djvs/m0116/m0116.kicad_sch

## KiCad design m0116.kicad_sch (2023-02-25)

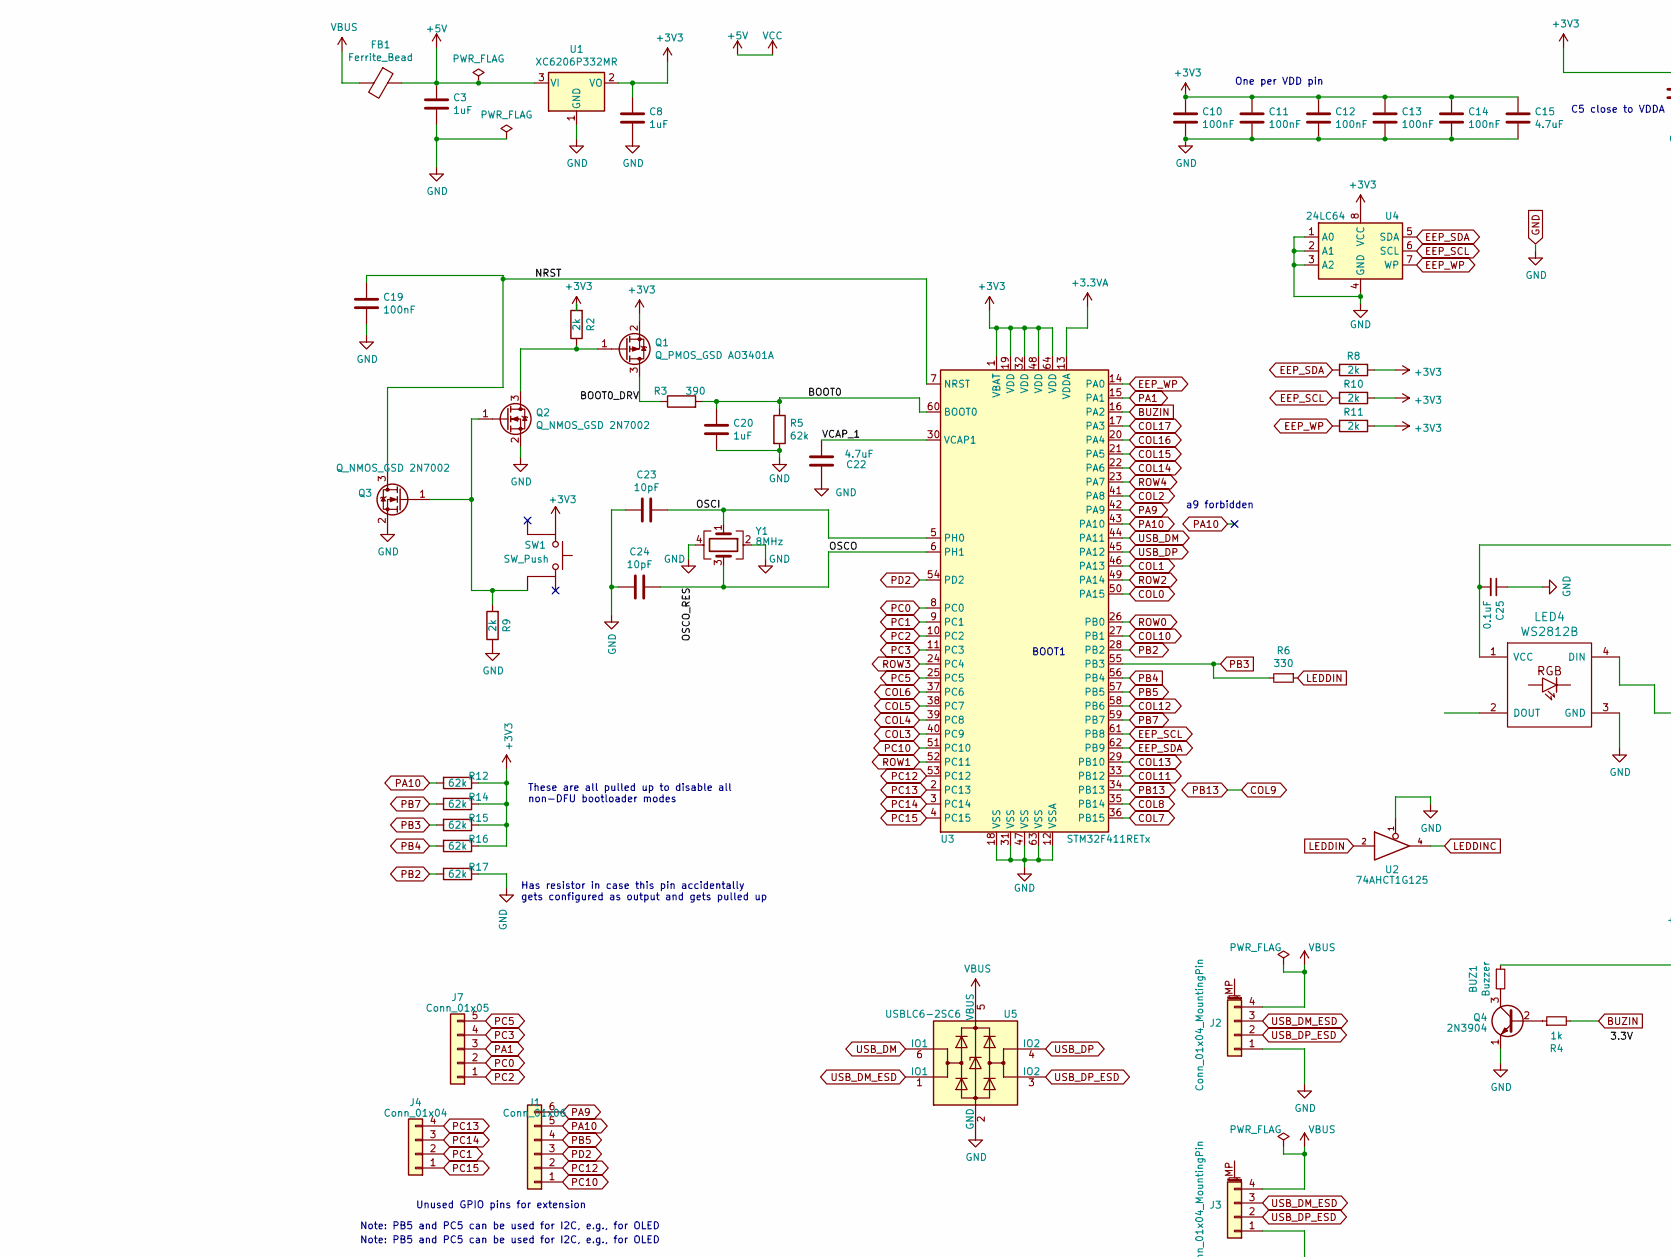
[picture p10: schematic m0116.kicad_sch, part in row 1, column 1]

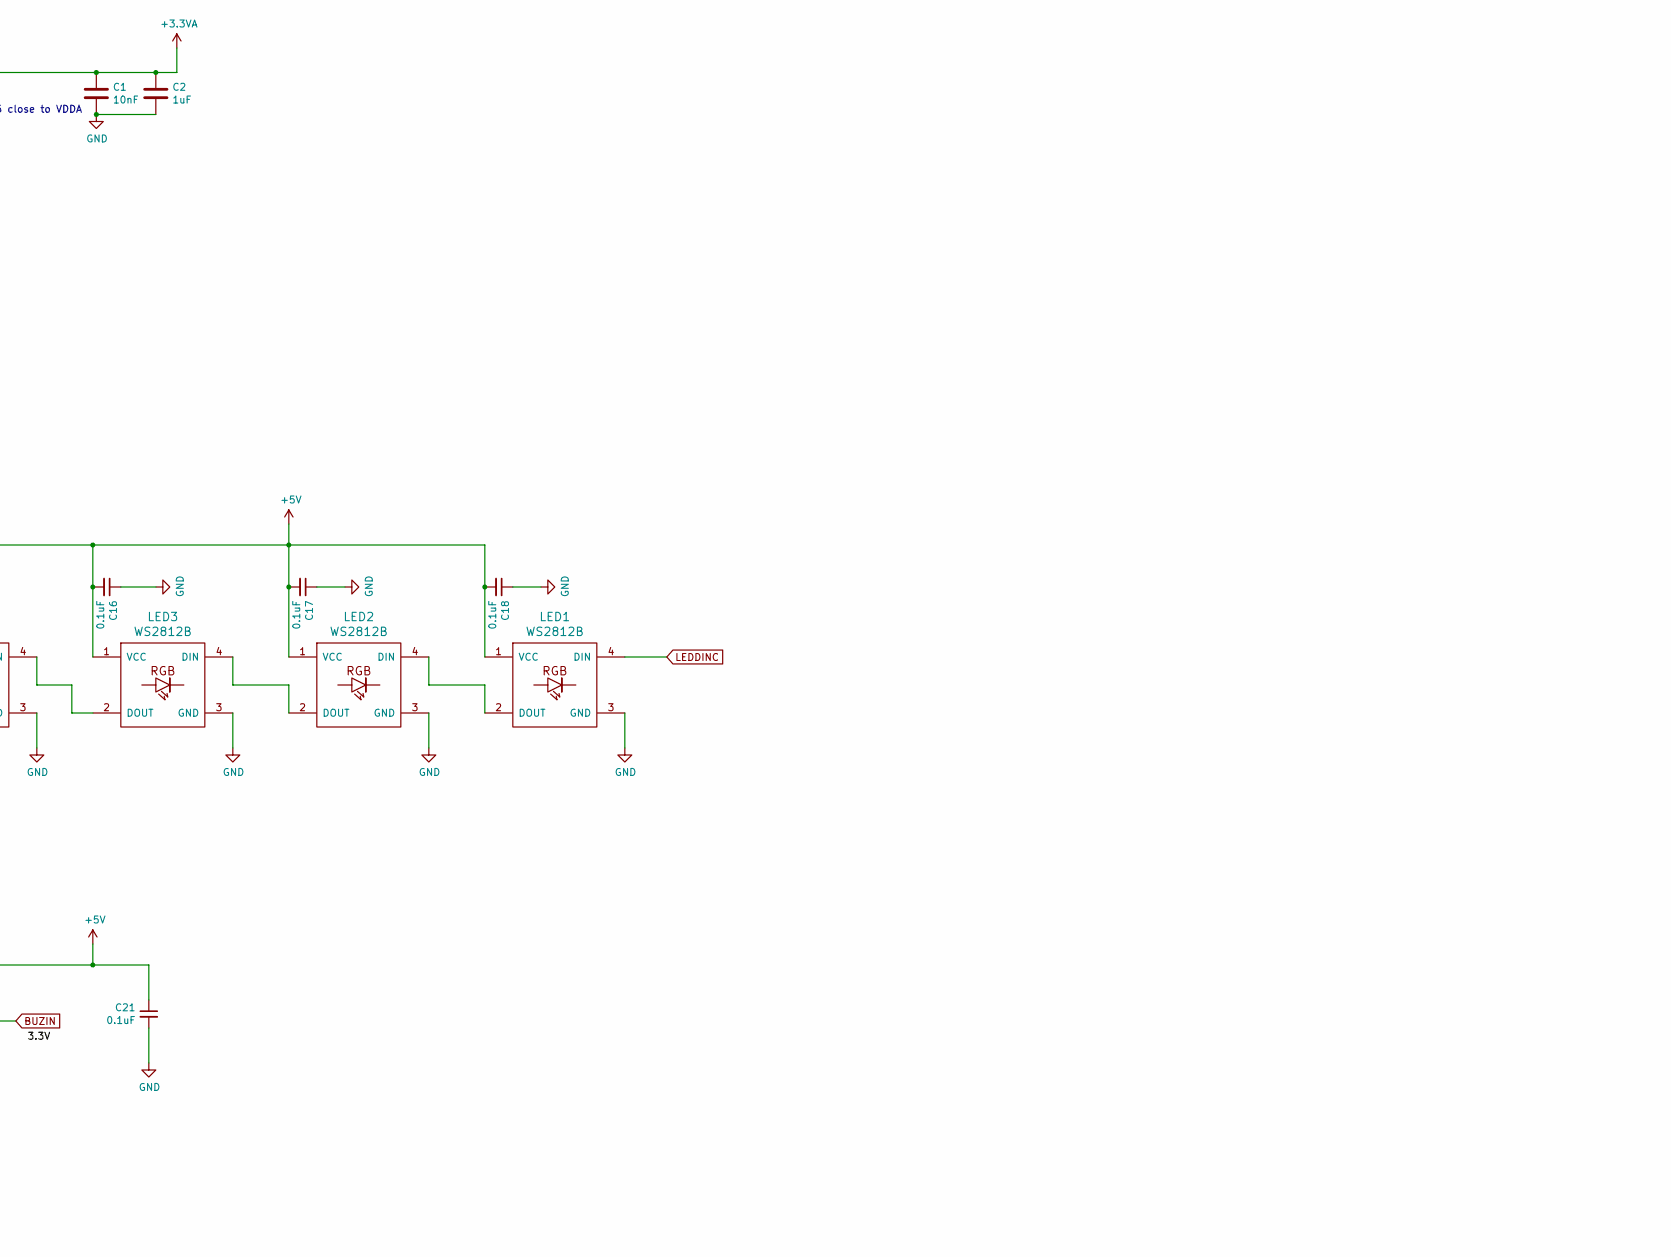
[picture p11: schematic m0116.kicad_sch, part in row 1, column 2]

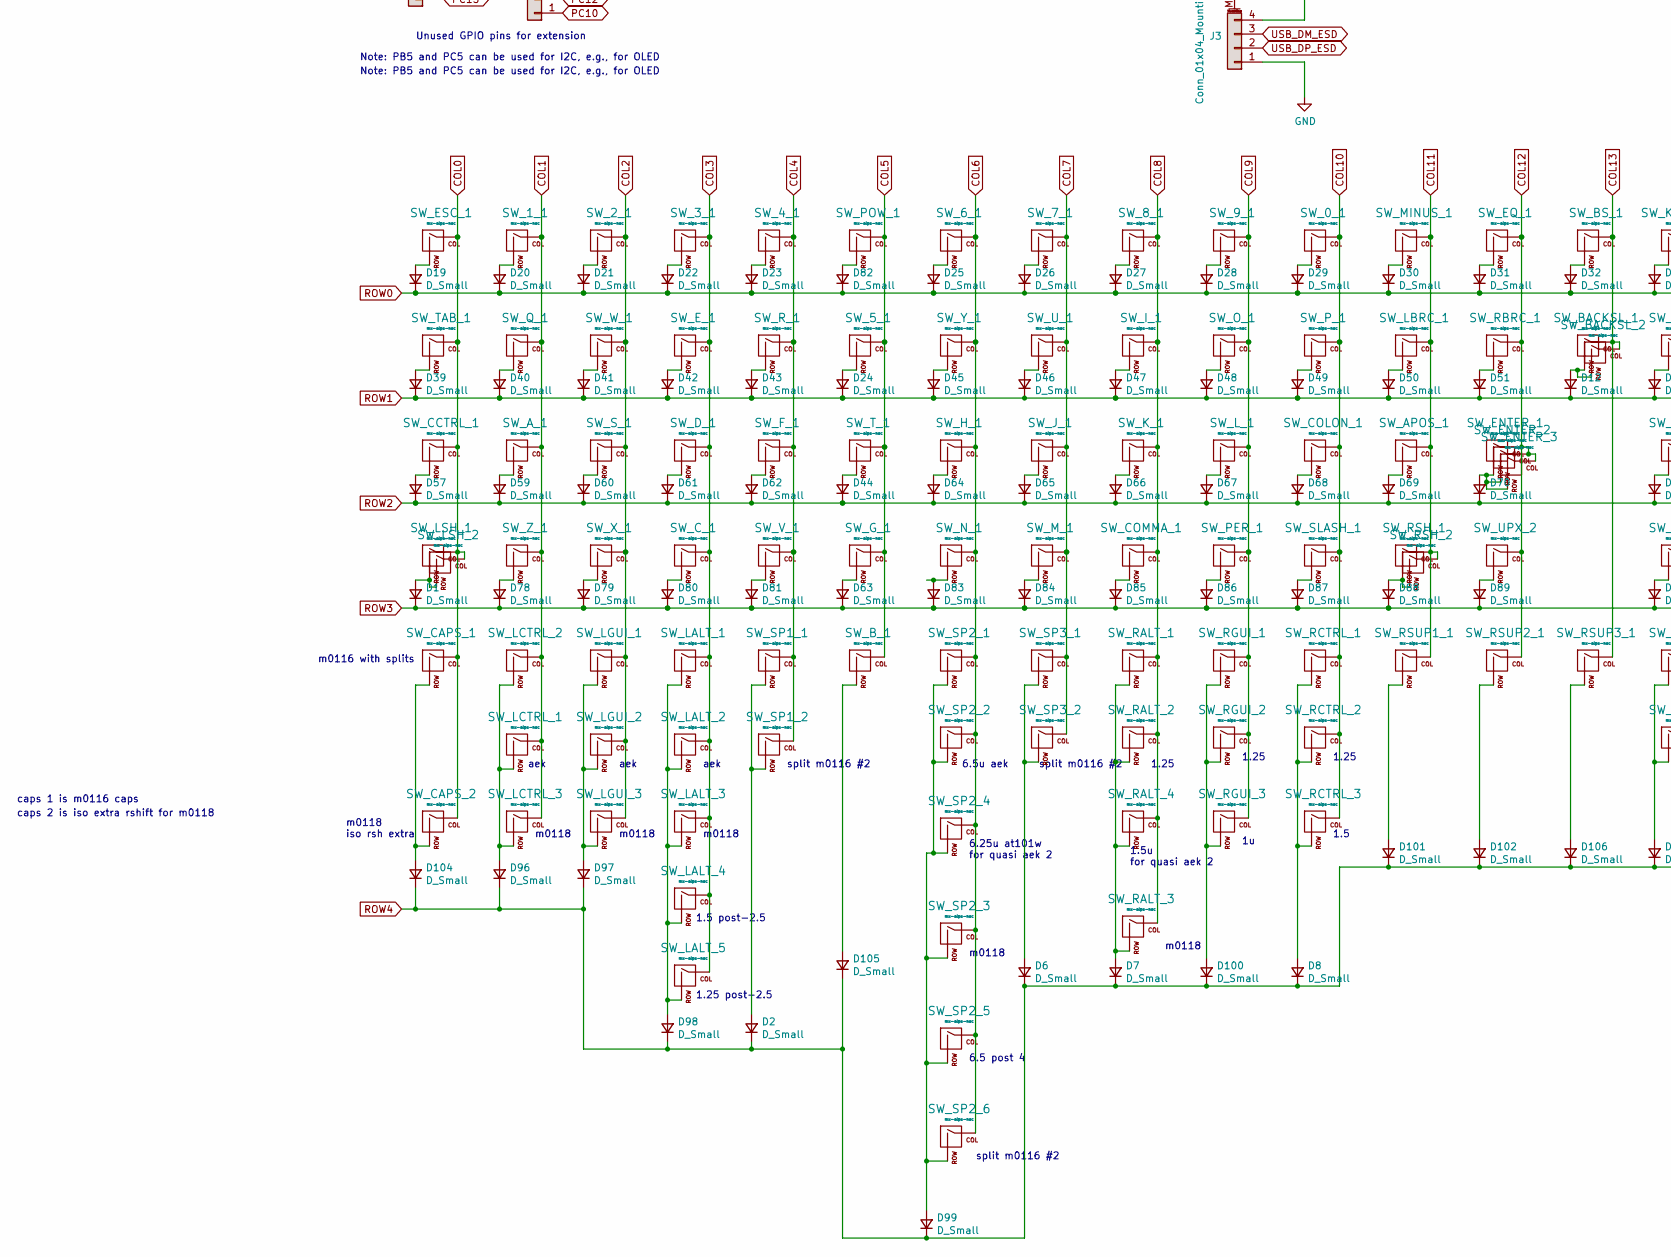
[picture p12: schematic m0116.kicad_sch, part in row 2, column 1]

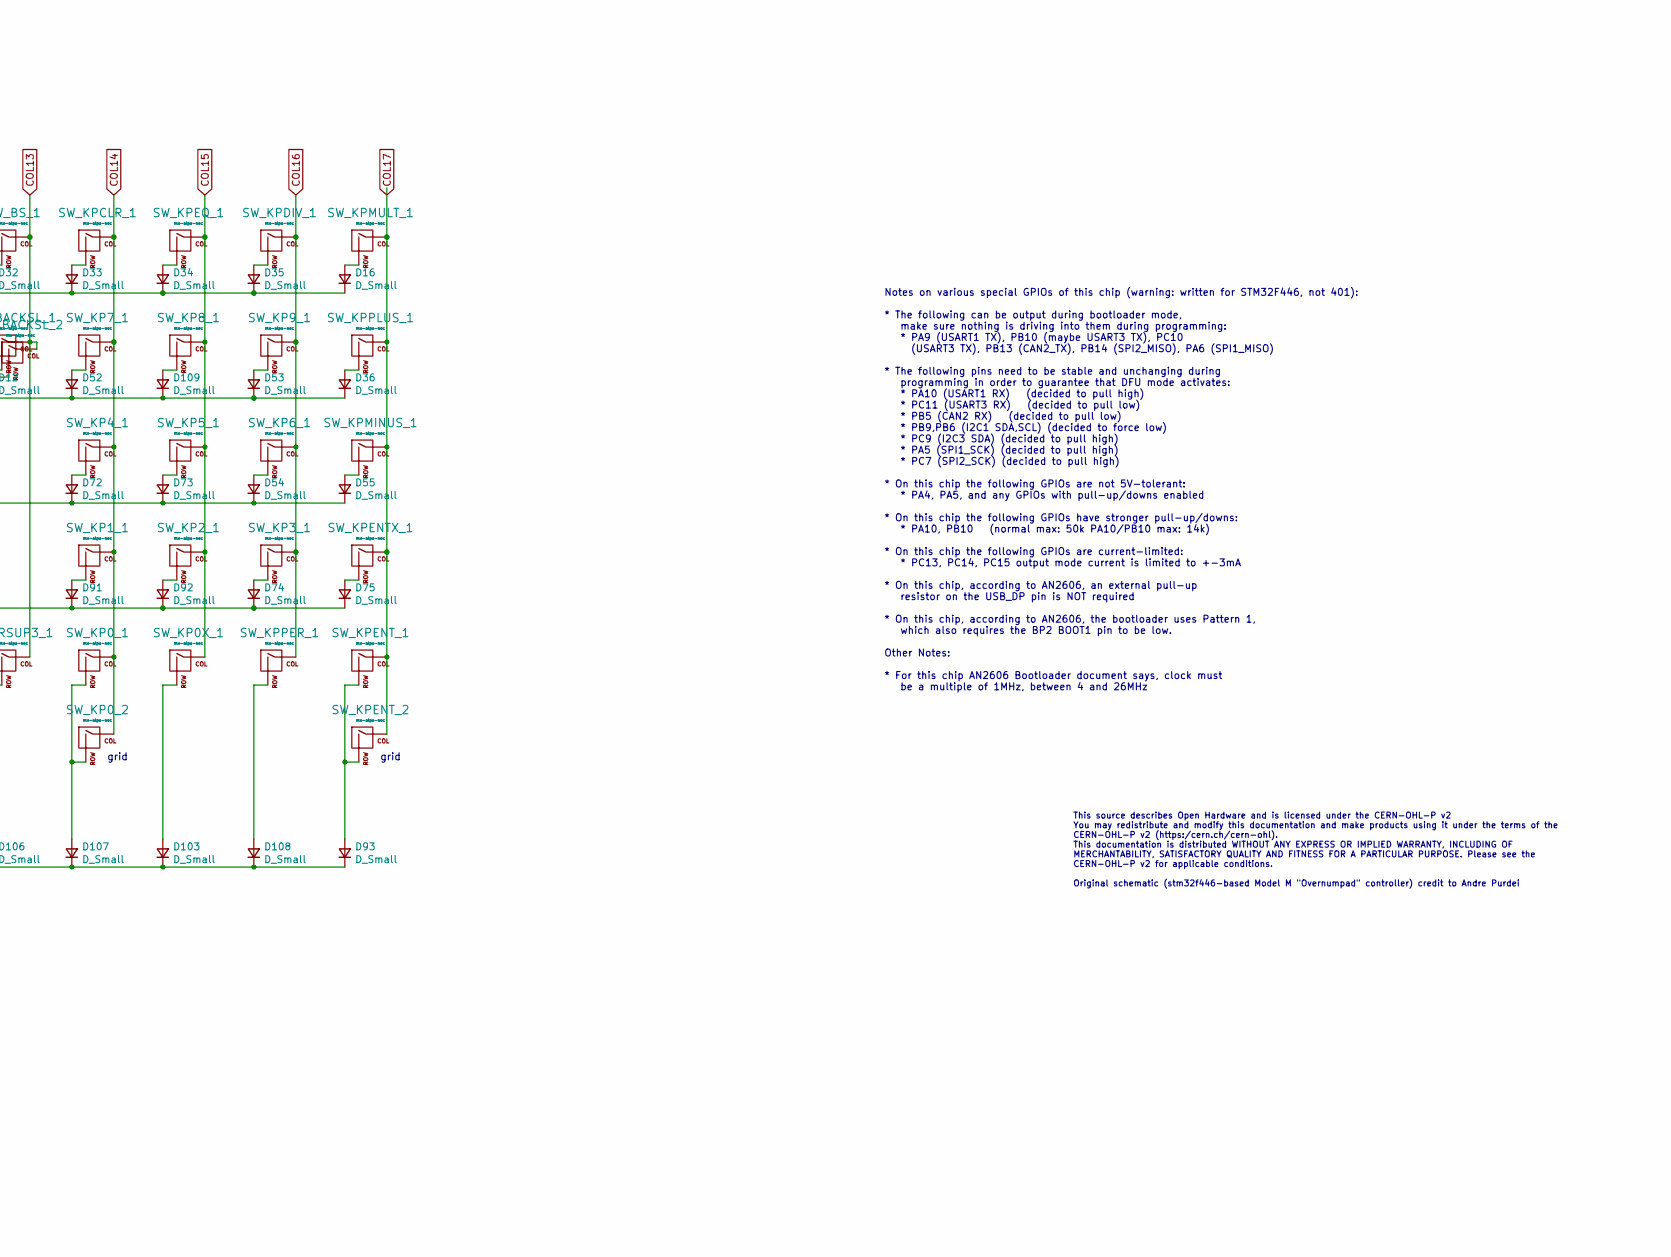
[picture p13: schematic m0116.kicad_sch, part in row 2, column 2]

Parts:
BUZ1: Buzzer; Buzzer_Mallory_AST1109MLTRQ
C1: 10nF; C_0805_2012Metric_Pad1.18x1.45mm_HandSolder; LCSC C1710
C2, C3, C20: 1uF; C_0805_2012Metric_Pad1.18x1.45mm_HandSolder; LCSC C28323
C8: 1uF; C_0805_2012Metric_Pad1.18x1.45mm_HandSolder; LCSC C49678
C10, C11, C12, C13, C14, C19: 100nF; C_0805_2012Metric_Pad1.18x1.45mm_HandSolder; LCSC C49678
C15, C22: 4.7uF; C_0805_2012Metric_Pad1.18x1.45mm_HandSolder; LCSC C1779
C16, C17, C18, C21, C25: 0.1uF; C_0805_2012Metric
C23, C24: 10pF; C_0805_2012Metric_Pad1.18x1.45mm_HandSolder; LCSC C1785
D1, D2, D6, D7, D8, D12, D16, D19, D20, D21, D22, D23, D24, D25, D26, D27, D28, D29, D30, D31, D32, D33, D34, D35, D36, D39, D40, D41, D42, D43, D44, D45, D46, D47, D48, D49, D50, D51, D52, D53, D54, D55, D57, D59, D60, D61, D62, D63, D64, D65, D66, D67, D68, D69, D70, D72, D73, D74, D75, D78, D79, D80, D81, D82, D83, D84, D85, D86, D87, D88, D89, D91, D92, D93, D96, D97, D98, D99, D100, D101, D102, D103, D104, D105, D106, D107, D108, D109: D_Small; D_SOD-123
FB1: Ferrite_Bead; L_0805_2012Metric_Pad1.15x1.40mm_HandSolder; LCSC C1015
J1: Conn_01x06; PinHeader_1x06_P1.27mm_Vertical
J2, J3: Conn_01x04_MountingPin; JST_SH_SM04B-SRSS-TB_1x04-1MP_P1.00mm_Horizontal
J4: Conn_01x04; PinHeader_1x04_P1.27mm_Vertical
J7: Conn_01x05; PinHeader_1x05_P1.27mm_Vertical
LED1, LED2, LED3, LED4: WS2812B; WS2812BDual
Q1: Q_PMOS_GSD AO3401A; SOT-23; LCSC C700954
Q2, Q3: Q_NMOS_GSD 2N7002; SOT-23; LCSC C8545
Q4: 2N3904; SOT-23
R2, R8, R9, R10, R11: 2k; R_0805_2012Metric_Pad1.20x1.40mm_HandSolder; LCSC C17604
R3: 390; R_0805_2012Metric_Pad1.20x1.40mm_HandSolder; LCSC C17655
R4: 1k; R_0805_2012Metric
R5, R12, R14, R15, R16, R17: 62k; R_0805_2012Metric_Pad1.20x1.40mm_HandSolder; LCSC C17783
R6: 330; R_0805_2012Metric
SW1: SW_Push; switch_K2-1187SQ-A4SW-06; LCSC C92584
SW_0_1, SW_1_1, SW_2_1, SW_3_1, SW_4_1, SW_5_1, SW_6_1, SW_7_1, SW_8_1, SW_9_1: mx-alps-nec; ALPS-1U
SW_APOS_1: mx-alps-nec; ALPS-1U
SW_A_1: mx-alps-nec; ALPS-1U
SW_BACKSL_1, SW_BACKSL_2: mx-alps-nec; ALPS-1U
SW_BS_1: mx-alps-nec; ALPS-1U
SW_B_1: mx-alps-nec; ALPS-1U
SW_CAPS_1, SW_CAPS_2: mx-alps-nec; ALPS-1U
SW_CCTRL_1: mx-alps-nec; ALPS-1U
SW_COLON_1: mx-alps-nec; ALPS-1U
SW_COMMA_1: mx-alps-nec; ALPS-1U
SW_C_1: mx-alps-nec; ALPS-1U
SW_D_1: mx-alps-nec; ALPS-1U
SW_ENTER_1, SW_ENTER_2, SW_ENTER_3: mx-alps-nec; ALPS-1U
SW_EQ_1: mx-alps-nec; ALPS-1U
SW_ESC_1: mx-alps-nec; ALPS-1U
SW_E_1: mx-alps-nec; ALPS-1U
SW_F_1: mx-alps-nec; ALPS-1U
SW_G_1: mx-alps-nec; ALPS-1U
SW_H_1: mx-alps-nec; ALPS-1U
SW_I_1: mx-alps-nec; ALPS-1U
SW_J_1: mx-alps-nec; ALPS-1U
SW_KP0X_1, SW_KP0_1, SW_KP0_2, SW_KP1_1, SW_KP2_1, SW_KP3_1, SW_KP4_1, SW_KP5_1, SW_KP6_1, SW_KP7_1, SW_KP8_1, SW_KP9_1: mx-alps-nec; ALPS-1U
SW_KPCLR_1: mx-alps-nec; ALPS-1U
SW_KPDIV_1: mx-alps-nec; ALPS-1U
SW_KPENTX_1: mx-alps-nec; ALPS-1U
SW_KPENT_1, SW_KPENT_2: mx-alps-nec; ALPS-1U
SW_KPEQ_1: mx-alps-nec; ALPS-1U
SW_KPMINUS_1: mx-alps-nec; ALPS-1U
SW_KPMULT_1: mx-alps-nec; ALPS-1U
SW_KPPER_1: mx-alps-nec; ALPS-1U
SW_KPPLUS_1: mx-alps-nec; ALPS-1U
SW_K_1: mx-alps-nec; ALPS-1U
SW_LALT_1, SW_LALT_2, SW_LALT_3, SW_LALT_4, SW_LALT_5: mx-alps-nec; ALPS-1U
SW_LBRC_1: mx-alps-nec; ALPS-1U
SW_LCTRL_1, SW_LCTRL_2, SW_LCTRL_3: mx-alps-nec; ALPS-1U
SW_LGUI_1, SW_LGUI_2, SW_LGUI_3: mx-alps-nec; ALPS-1U
SW_LSH_1, SW_LSH_2: mx-alps-nec; ALPS-1U
SW_L_1: mx-alps-nec; ALPS-1U
SW_MINUS_1: mx-alps-nec; ALPS-1U
SW_M_1: mx-alps-nec; ALPS-1U
SW_N_1: mx-alps-nec; ALPS-1U
SW_O_1: mx-alps-nec; ALPS-1U
SW_PER_1: mx-alps-nec; ALPS-1U
SW_POW_1: mx-alps-nec; ALPS-1U
SW_P_1: mx-alps-nec; ALPS-1U
SW_Q_1: mx-alps-nec; ALPS-1U
SW_RALT_1, SW_RALT_2, SW_RALT_3, SW_RALT_4: mx-alps-nec; ALPS-1U
SW_RBRC_1: mx-alps-nec; ALPS-1U
SW_RCTRL_1, SW_RCTRL_2, SW_RCTRL_3: mx-alps-nec; ALPS-1U
SW_RGUI_1, SW_RGUI_2, SW_RGUI_3: mx-alps-nec; ALPS-1U
SW_RSH_1, SW_RSH_2: mx-alps-nec; ALPS-1U
SW_RSUP1_1, SW_RSUP2_1, SW_RSUP3_1: mx-alps-nec; ALPS-1U
SW_R_1: mx-alps-nec; ALPS-1U
SW_SLASH_1: mx-alps-nec; ALPS-1U
SW_SP1_1, SW_SP1_2, SW_SP2_1, SW_SP2_2, SW_SP2_3, SW_SP2_4, SW_SP2_5, SW_SP2_6, SW_SP3_1, SW_SP3_2: mx-alps-nec; ALPS-1U
SW_S_1: mx-alps-nec; ALPS-1U
SW_TAB_1: mx-alps-nec; ALPS-1U
SW_T_1: mx-alps-nec; ALPS-1U
SW_UPX_2: mx-alps-nec; ALPS-1U
SW_U_1: mx-alps-nec; ALPS-1U
SW_V_1: mx-alps-nec; ALPS-1U
SW_W_1: mx-alps-nec; ALPS-1U
SW_X_1: mx-alps-nec; ALPS-1U
SW_Y_1: mx-alps-nec; ALPS-1U
SW_Z_1: mx-alps-nec; ALPS-1U
U1: XC6206P332MR; SOT-23_Handsoldering; LCSC C6186
U2: 74AHCT1G125; SOT-23-5
U3: STM32F411RETx; LQFP-64_10x10mm_P0.5mm; LCSC C69336
U4: 24LC64; SOIC-8_3.9x4.9mm_P1.27mm; LCSC C79988
U5: USBLC6-2SC6; SOT-23-6; LCSC C7519
Y1: 8MHz; Crystal_SMD_3225-4Pin_3.2x2.5mm; LCSC C389817

Connections:
+3.3VA: C1.1, C2.1, C8.1, C10.1, C11.1, C12.1, C13.1, C14.1, C15.1, Q1.2 (S), R2.2, R8.1, R10.1, R11.1, R12.1, R14.1, R15.1, R16.1, SW1.1, U1.2 (VO), U3.1 (VBAT), U3.13 (VDDA), U3.19 (VDD), U3.32 (VDD), U3.48 (VDD), U3.64 (VDD), U4.8 (VCC)
+5V: BUZ1.1, C3.1, C16.2, C17.2, C18.2, C21.1, C25.2, FB1.1, LED1.1 (VCC), LED2.1 (VCC), LED3.1 (VCC), LED4.1 (VCC), U1.3 (VI)
BOOT0: C20.1, R3.2, R5.1, U3.60 (BOOT0)
BOOT0_DRV: Q1.3 (D), R3.1
BUZIN: R4.2, U3.16 (PA2)
COL0: SW_CAPS_1.1 (COL), SW_CAPS_2.1 (COL), SW_CCTRL_1.1 (COL), SW_ESC_1.1 (COL), SW_LSH_1.1 (COL), SW_LSH_2.1 (COL), SW_TAB_1.1 (COL), U3.50 (PA15)
COL1: SW_1_1.1 (COL), SW_A_1.1 (COL), SW_LCTRL_1.1 (COL), SW_LCTRL_2.1 (COL), SW_LCTRL_3.1 (COL), SW_Q_1.1 (COL), SW_Z_1.1 (COL), U3.46 (PA13)
COL2: SW_2_1.1 (COL), SW_LGUI_1.1 (COL), SW_LGUI_2.1 (COL), SW_LGUI_3.1 (COL), SW_S_1.1 (COL), SW_W_1.1 (COL), SW_X_1.1 (COL), U3.41 (PA8)
COL3: SW_3_1.1 (COL), SW_C_1.1 (COL), SW_D_1.1 (COL), SW_E_1.1 (COL), SW_LALT_1.1 (COL), SW_LALT_2.1 (COL), SW_LALT_3.1 (COL), SW_LALT_4.1 (COL), SW_LALT_5.1 (COL), U3.40 (PC9)
COL4: SW_4_1.1 (COL), SW_F_1.1 (COL), SW_R_1.1 (COL), SW_SP1_1.1 (COL), SW_SP1_2.1 (COL), SW_V_1.1 (COL), U3.39 (PC8)
COL5: SW_5_1.1 (COL), SW_B_1.1 (COL), SW_G_1.1 (COL), SW_POW_1.1 (COL), SW_T_1.1 (COL), U3.38 (PC7)
COL6: SW_6_1.1 (COL), SW_H_1.1 (COL), SW_N_1.1 (COL), SW_SP2_1.1 (COL), SW_SP2_2.1 (COL), SW_SP2_3.1 (COL), SW_SP2_4.1 (COL), SW_SP2_5.1 (COL), SW_SP2_6.1 (COL), SW_Y_1.1 (COL), U3.37 (PC6)
COL7: SW_7_1.1 (COL), SW_J_1.1 (COL), SW_M_1.1 (COL), SW_SP3_1.1 (COL), SW_SP3_2.1 (COL), SW_U_1.1 (COL), U3.36 (PB15)
COL8: SW_8_1.1 (COL), SW_COMMA_1.1 (COL), SW_I_1.1 (COL), SW_K_1.1 (COL), SW_RALT_1.1 (COL), SW_RALT_2.1 (COL), SW_RALT_3.1 (COL), SW_RALT_4.1 (COL), U3.35 (PB14)
COL9: SW_9_1.1 (COL), SW_L_1.1 (COL), SW_O_1.1 (COL), SW_PER_1.1 (COL), SW_RGUI_1.1 (COL), SW_RGUI_2.1 (COL), SW_RGUI_3.1 (COL), U3.34 (PB13)
COL10: SW_0_1.1 (COL), SW_COLON_1.1 (COL), SW_P_1.1 (COL), SW_RCTRL_1.1 (COL), SW_RCTRL_2.1 (COL), SW_RCTRL_3.1 (COL), SW_SLASH_1.1 (COL), U3.27 (PB1)
COL11: SW_APOS_1.1 (COL), SW_LBRC_1.1 (COL), SW_MINUS_1.1 (COL), SW_RSH_1.1 (COL), SW_RSH_2.1 (COL), SW_RSUP1_1.1 (COL), U3.33 (PB12)
COL12: SW_ENTER_1.1 (COL), SW_ENTER_2.1 (COL), SW_ENTER_3.1 (COL), SW_EQ_1.1 (COL), SW_RBRC_1.1 (COL), SW_RSUP2_1.1 (COL), SW_UPX_2.1 (COL), U3.58 (PB6)
COL13: SW_BACKSL_1.1 (COL), SW_BACKSL_2.1 (COL), SW_BS_1.1 (COL), SW_RSUP3_1.1 (COL), U3.29 (PB10)
COL14: SW_KP0_1.1 (COL), SW_KP0_2.1 (COL), SW_KP1_1.1 (COL), SW_KP4_1.1 (COL), SW_KP7_1.1 (COL), SW_KPCLR_1.1 (COL), U3.22 (PA6)
COL15: SW_KP0X_1.1 (COL), SW_KP2_1.1 (COL), SW_KP5_1.1 (COL), SW_KP8_1.1 (COL), SW_KPEQ_1.1 (COL), U3.21 (PA5)
COL16: SW_KP3_1.1 (COL), SW_KP6_1.1 (COL), SW_KP9_1.1 (COL), SW_KPDIV_1.1 (COL), SW_KPPER_1.1 (COL), U3.20 (PA4)
COL17: SW_KPENTX_1.1 (COL), SW_KPENT_1.1 (COL), SW_KPENT_2.1 (COL), SW_KPMINUS_1.1 (COL), SW_KPMULT_1.1 (COL), SW_KPPLUS_1.1 (COL), U3.17 (PA3)
EEP_SCL: R10.2, U3.61 (PB8), U4.6 (SCL)
EEP_SDA: R8.2, U3.62 (PB9), U4.5 (SDA)
EEP_WP: R11.2, U3.14 (PA0), U4.7 (WP)
GND: C1.2, C2.2, C3.2, C8.2, C10.2, C11.2, C12.2, C13.2, C14.2, C15.2, C16.1, C17.1, C18.1, C19.1, C20.2, C21.2, C22.2, C23.2, C24.2, C25.1, J2.1, J3.1, LED1.3 (GND), LED2.3 (GND), LED3.3 (GND), LED4.3 (GND), Q2.2 (S), Q3.2 (S), Q4.1 (E), R5.2, R9.1, R17.1, U1.1 (GND), U2.1, U3.12 (VSSA), U3.18 (VSS), U3.31 (VSS), U3.47 (VSS), U3.63 (VSS), U4.1 (A0), U4.2 (A1), U4.3 (A2), U4.4 (GND), U5.2 (GND), Y1.2, Y1.4
LEDDIN: R6.1, U2.2
LEDDINC: LED1.4 (DIN), U2.4
NRST: C19.2, Q3.3 (D), U3.7 (NRST)
unnamed: BUZ1.2, Q4.3 (C)
unnamed: D1.2 (A), SW_LSH_1.2 (ROW), SW_LSH_2.2 (ROW)
unnamed: D2.2 (A), SW_SP1_1.2 (ROW), SW_SP1_2.2 (ROW)
unnamed: D6.2 (A), SW_SP3_1.2 (ROW), SW_SP3_2.2 (ROW)
unnamed: D7.2 (A), SW_RALT_1.2 (ROW), SW_RALT_2.2 (ROW), SW_RALT_3.2 (ROW), SW_RALT_4.2 (ROW)
unnamed: D8.2 (A), SW_RCTRL_1.2 (ROW), SW_RCTRL_2.2 (ROW), SW_RCTRL_3.2 (ROW)
unnamed: D12.2 (A), SW_BACKSL_1.2 (ROW), SW_BACKSL_2.2 (ROW)
unnamed: D16.2 (A), SW_KPMULT_1.2 (ROW)
unnamed: D19.2 (A), SW_ESC_1.2 (ROW)
unnamed: D20.2 (A), SW_1_1.2 (ROW)
unnamed: D21.2 (A), SW_2_1.2 (ROW)
unnamed: D22.2 (A), SW_3_1.2 (ROW)
unnamed: D23.2 (A), SW_4_1.2 (ROW)
unnamed: D24.2 (A), SW_5_1.2 (ROW)
unnamed: D25.2 (A), SW_6_1.2 (ROW)
unnamed: D26.2 (A), SW_7_1.2 (ROW)
unnamed: D27.2 (A), SW_8_1.2 (ROW)
unnamed: D28.2 (A), SW_9_1.2 (ROW)
unnamed: D29.2 (A), SW_0_1.2 (ROW)
unnamed: D30.2 (A), SW_MINUS_1.2 (ROW)
unnamed: D31.2 (A), SW_EQ_1.2 (ROW)
unnamed: D32.2 (A), SW_BS_1.2 (ROW)
unnamed: D33.2 (A), SW_KPCLR_1.2 (ROW)
unnamed: D34.2 (A), SW_KPEQ_1.2 (ROW)
unnamed: D35.2 (A), SW_KPDIV_1.2 (ROW)
unnamed: D36.2 (A), SW_KPPLUS_1.2 (ROW)
unnamed: D39.2 (A), SW_TAB_1.2 (ROW)
unnamed: D40.2 (A), SW_Q_1.2 (ROW)
unnamed: D41.2 (A), SW_W_1.2 (ROW)
unnamed: D42.2 (A), SW_E_1.2 (ROW)
unnamed: D43.2 (A), SW_R_1.2 (ROW)
unnamed: D44.2 (A), SW_T_1.2 (ROW)
unnamed: D45.2 (A), SW_Y_1.2 (ROW)
unnamed: D46.2 (A), SW_U_1.2 (ROW)
unnamed: D47.2 (A), SW_I_1.2 (ROW)
unnamed: D48.2 (A), SW_O_1.2 (ROW)
unnamed: D49.2 (A), SW_P_1.2 (ROW)
unnamed: D50.2 (A), SW_LBRC_1.2 (ROW)
unnamed: D51.2 (A), SW_RBRC_1.2 (ROW)
unnamed: D52.2 (A), SW_KP7_1.2 (ROW)
unnamed: D53.2 (A), SW_KP9_1.2 (ROW)
unnamed: D54.2 (A), SW_KP6_1.2 (ROW)
unnamed: D55.2 (A), SW_KPMINUS_1.2 (ROW)
unnamed: D57.2 (A), SW_CCTRL_1.2 (ROW)
unnamed: D59.2 (A), SW_A_1.2 (ROW)
unnamed: D60.2 (A), SW_S_1.2 (ROW)
unnamed: D61.2 (A), SW_D_1.2 (ROW)
unnamed: D62.2 (A), SW_F_1.2 (ROW)
unnamed: D63.2 (A), SW_G_1.2 (ROW)
unnamed: D64.2 (A), SW_H_1.2 (ROW)
unnamed: D65.2 (A), SW_J_1.2 (ROW)
unnamed: D66.2 (A), SW_K_1.2 (ROW)
unnamed: D67.2 (A), SW_L_1.2 (ROW)
unnamed: D68.2 (A), SW_COLON_1.2 (ROW)
unnamed: D69.2 (A), SW_APOS_1.2 (ROW)
unnamed: D70.2 (A), SW_ENTER_1.2 (ROW), SW_ENTER_2.2 (ROW), SW_ENTER_3.2 (ROW)
unnamed: D72.2 (A), SW_KP4_1.2 (ROW)
unnamed: D73.2 (A), SW_KP5_1.2 (ROW)
unnamed: D74.2 (A), SW_KP3_1.2 (ROW)
unnamed: D75.2 (A), SW_KPENTX_1.2 (ROW)
unnamed: D78.2 (A), SW_Z_1.2 (ROW)
unnamed: D79.2 (A), SW_X_1.2 (ROW)
unnamed: D80.2 (A), SW_C_1.2 (ROW)
unnamed: D81.2 (A), SW_V_1.2 (ROW)
unnamed: D82.2 (A), SW_POW_1.2 (ROW)
unnamed: D83.2 (A), SW_N_1.2 (ROW)
unnamed: D84.2 (A), SW_M_1.2 (ROW)
unnamed: D85.2 (A), SW_COMMA_1.2 (ROW)
unnamed: D86.2 (A), SW_PER_1.2 (ROW)
unnamed: D87.2 (A), SW_SLASH_1.2 (ROW)
unnamed: D88.2 (A), SW_RSH_1.2 (ROW), SW_RSH_2.2 (ROW)
unnamed: D89.2 (A), SW_UPX_2.2 (ROW)
unnamed: D91.2 (A), SW_KP1_1.2 (ROW)
unnamed: D92.2 (A), SW_KP2_1.2 (ROW)
unnamed: D93.2 (A), SW_KPENT_1.2 (ROW), SW_KPENT_2.2 (ROW)
unnamed: D96.2 (A), SW_LCTRL_1.2 (ROW), SW_LCTRL_2.2 (ROW), SW_LCTRL_3.2 (ROW)
unnamed: D97.2 (A), SW_LGUI_1.2 (ROW), SW_LGUI_2.2 (ROW), SW_LGUI_3.2 (ROW)
unnamed: D98.2 (A), SW_LALT_1.2 (ROW), SW_LALT_2.2 (ROW), SW_LALT_3.2 (ROW), SW_LALT_4.2 (ROW), SW_LALT_5.2 (ROW)
unnamed: D99.2 (A), SW_SP2_1.2 (ROW), SW_SP2_2.2 (ROW), SW_SP2_3.2 (ROW), SW_SP2_4.2 (ROW), SW_SP2_5.2 (ROW), SW_SP2_6.2 (ROW)
unnamed: D100.2 (A), SW_RGUI_1.2 (ROW), SW_RGUI_2.2 (ROW), SW_RGUI_3.2 (ROW)
unnamed: D101.2 (A), SW_RSUP1_1.2 (ROW)
unnamed: D102.2 (A), SW_RSUP2_1.2 (ROW)
unnamed: D103.2 (A), SW_KP0X_1.2 (ROW)
unnamed: D104.2 (A), SW_CAPS_1.2 (ROW), SW_CAPS_2.2 (ROW)
unnamed: D105.2 (A), SW_B_1.2 (ROW)
unnamed: D106.2 (A), SW_RSUP3_1.2 (ROW)
unnamed: D107.2 (A), SW_KP0_1.2 (ROW), SW_KP0_2.2 (ROW)
unnamed: D108.2 (A), SW_KPPER_1.2 (ROW)
unnamed: D109.2 (A), SW_KP8_1.2 (ROW)
unnamed: LED1.2 (DOUT), LED2.4 (DIN)
unnamed: LED2.2 (DOUT), LED3.4 (DIN)
unnamed: LED3.2 (DOUT), LED4.4 (DIN)
unnamed: Q1.1 (G), Q2.3 (D), R2.1
unnamed: Q2.1 (G), Q3.1 (G), R9.2, SW1.4
unnamed: Q4.2 (B), R4.1
OSCI: C23.1, U3.5 (PH0), Y1.1
OSCO: C24.1, U3.6 (PH1), Y1.3
PA1: J7.3, U3.15 (PA1)
PA9: J1.6, U3.42 (PA9)
PA10: J1.5, R12.2, U3.43 (PA10)
PB2: R17.2, U3.28 (PB2)
PB3: R6.2, R15.2, U3.55 (PB3)
PB4: R16.2, U3.56 (PB4)
PB5: J1.4, U3.57 (PB5)
PB7: R14.2, U3.59 (PB7)
PC0: J7.2, U3.8 (PC0)
PC1: J4.2, U3.9 (PC1)
PC2: J7.1, U3.10 (PC2)
PC3: J7.4, U3.11 (PC3)
PC5: J7.5, U3.25 (PC5)
PC10: J1.1, U3.51 (PC10)
PC12: J1.2, U3.53 (PC12)
PC13: J4.4, U3.2 (PC13)
PC14: J4.3, U3.3 (PC14)
PC15: J4.1, U3.4 (PC15)
PD2: J1.3, U3.54 (PD2)
ROW0: D16.1 (K), D19.1 (K), D20.1 (K), D21.1 (K), D22.1 (K), D23.1 (K), D25.1 (K), D26.1 (K), D27.1 (K), D28.1 (K), D29.1 (K), D30.1 (K), D31.1 (K), D32.1 (K), D33.1 (K), D34.1 (K), D35.1 (K), D82.1 (K), U3.26 (PB0)
ROW1: D12.1 (K), D24.1 (K), D36.1 (K), D39.1 (K), D40.1 (K), D41.1 (K), D42.1 (K), D43.1 (K), D45.1 (K), D46.1 (K), D47.1 (K), D48.1 (K), D49.1 (K), D50.1 (K), D51.1 (K), D52.1 (K), D53.1 (K), D109.1 (K), U3.52 (PC11)
ROW2: D44.1 (K), D54.1 (K), D55.1 (K), D57.1 (K), D59.1 (K), D60.1 (K), D61.1 (K), D62.1 (K), D64.1 (K), D65.1 (K), D66.1 (K), D67.1 (K), D68.1 (K), D69.1 (K), D70.1 (K), D72.1 (K), D73.1 (K), U3.49 (PA14)
ROW3: D1.1 (K), D63.1 (K), D74.1 (K), D75.1 (K), D78.1 (K), D79.1 (K), D80.1 (K), D81.1 (K), D83.1 (K), D84.1 (K), D85.1 (K), D86.1 (K), D87.1 (K), D88.1 (K), D89.1 (K), D91.1 (K), D92.1 (K), U3.24 (PC4)
ROW4: D2.1 (K), D6.1 (K), D7.1 (K), D8.1 (K), D93.1 (K), D96.1 (K), D97.1 (K), D98.1 (K), D99.1 (K), D100.1 (K), D101.1 (K), D102.1 (K), D103.1 (K), D104.1 (K), D105.1 (K), D106.1 (K), D107.1 (K), D108.1 (K), U3.23 (PA7)
USB_DM: U3.44 (PA11), U5.6 (IO1)
USB_DM_ESD: J2.3, J3.3, U5.1 (IO1)
USB_DP: U3.45 (PA12), U5.4 (IO2)
USB_DP_ESD: J2.2, J3.2, U5.3 (IO2)
VBUS: FB1.2, J2.4, J3.4, U5.5 (VBUS)
VCAP_1: C22.1, U3.30 (VCAP1)

Notes on the sheet:
m0118
Note: PB5 and PC5 can be used for I2C, e.g., for OLED
One per VDD pin
split m0116 #2
aek
m0116 with splits
6.25u at101w for quasi aek 2
split m0116 #2
6.5u aek
1.5 post-2.5
6.5 post 4
This source describes Open Hardware and is licensed under the CERN-OHL-P v2 You may redistribute and modify this documentation and make products using it under the terms of the CERN-OHL-P v2 (https:/cern.ch/cern-ohl). This documentation is distributed WITHOUT ANY EXPRESS OR IMPLIED WARRANTY, INCLUD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
a9 forbidden
Notes on various special GPIOs of this chip (warning: written for STM32F446, not 401): * The following can be output during bootloader mode, make sure nothing is driving into them during programming: * PA9 (USART1 TX), PB10 (maybe USART3 TX), PC10 (USART3 TX), PB13 (CAN2_TX), PB14 (SPI2_MISO), PA6 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
1.25
caps 2 is iso extra rshift for m0118
C5 close to VDDA
1.5
BOOT1
These are all pulled up to disable all non-DFU bootloader modes
m0118
1.5u for quasi aek 2
grid
caps 1 is m0116 caps
1.25
Has resistor in case this pin accidentally gets configured as output and gets pulled up
m0118 iso rsh extra
Unused GPIO pins for extension
1.25 post-2.5
